xeecos/OpenNightSkyCam/Firmware/src/ll_cam.cpp

// Copyright 2010-2020 Espressif Systems (Shanghai) PTE LTD
//
// Licensed under the Apache License, Version 2.0 (the "License");
// you may not use this file except in compliance with the License.
// You may obtain a copy of the License at
//
//     http://www.apache.org/licenses/LICENSE-2.0
//
// Unless required by applicable law or agreed to in writing, software
// distributed under the License is distributed on an "AS IS" BASIS,
// WITHOUT WARRANTIES OR CONDITIONS OF ANY KIND, either express or implied.
// See the License for the specific language governing permissions and
// limitations under the License.

#include <stdio.h>
#include <string.h>
#include <Arduino.h>
#include "soc/system_reg.h"
#include "soc/lcd_cam_struct.h"
#include "soc/lcd_cam_reg.h"
#include "soc/gdma_struct.h"
#include "soc/gdma_periph.h"
#include "soc/gdma_reg.h"
#include "ll_cam.h"
#include "cam_hal.h"
#include "config.h"
#include "log.h"
#if (ESP_IDF_VERSION_MAJOR >= 5)
#define gpio_matrix_in(a, b, c) gpio_iomux_in(a, b)
#define gpio_matrix_out(a, b, c, d) gpio_iomux_out(a, b, c)
#endif
static const char *TAG = "s3 ll_cam";
static uint8_t BIT12_8[4096] = {};
static void IRAM_ATTR ll_cam_vsync_isr(void *arg)
{
    // DBG_PIN_SET(1);
    cam_obj_t *cam = (cam_obj_t *)arg;
    BaseType_t HPTaskAwoken = pdFALSE;
    uint32_t state = LCD_CAM.lc_dma_int_st.val;
    uint32_t v = LCD_CAM.lc_dma_int_st.cam_vsync_int_st;
    if (state == 0)
    {
        return;
    }
    LCD_CAM.lc_dma_int_clr.val = state;
    if (v)
    {
        ll_cam_send_event(cam, CAM_VSYNC_EVENT, &HPTaskAwoken);
    }

    if (HPTaskAwoken == pdTRUE)
    {
        portYIELD_FROM_ISR();
    }
    // DBG_PIN_SET(0);
}

static void IRAM_ATTR ll_cam_dma_isr(void *arg)
{
    cam_obj_t *cam = (cam_obj_t *)arg;
    BaseType_t HPTaskAwoken = pdFALSE;
    int state = GDMA.channel[cam->dma_num].in.int_st.val;
    int v = GDMA.channel[cam->dma_num].in.int_st.in_suc_eof;
    if (state == 0)
    {
        return;
    }
    GDMA.channel[cam->dma_num].in.int_clr.val = state;
    if (v)
    {
        ll_cam_send_event(cam, CAM_IN_SUC_EOF_EVENT, &HPTaskAwoken);
    }

    if (HPTaskAwoken == pdTRUE)
    {
        portYIELD_FROM_ISR();
    }
}

bool IRAM_ATTR ll_cam_stop(cam_obj_t *cam)
{
    GDMA.channel[cam->dma_num].in.int_ena.in_suc_eof = 0;
    GDMA.channel[cam->dma_num].in.int_clr.in_suc_eof = 0;
    GDMA.channel[cam->dma_num].in.link.stop = 1;
    return true;
}

esp_err_t ll_cam_deinit(cam_obj_t *cam)
{
    if (cam->cam_intr_handle)
    {
        esp_intr_free(cam->cam_intr_handle);
        cam->cam_intr_handle = NULL;
    }

    if (cam->dma_intr_handle)
    {
        esp_intr_free(cam->dma_intr_handle);
        cam->dma_intr_handle = NULL;
    }
    GDMA.channel[cam->dma_num].in.link.addr = 0x0;

    LCD_CAM.cam_ctrl1.cam_start = 0;
    LCD_CAM.cam_ctrl1.cam_reset = 1;
    LCD_CAM.cam_ctrl1.cam_reset = 0;
    return ESP_OK;
}

bool ll_cam_start(cam_obj_t *cam, int frame_pos)
{

    LCD_CAM.cam_ctrl1.cam_start = 0;

    GDMA.channel[cam->dma_num].in.int_clr.in_suc_eof = 1;
    GDMA.channel[cam->dma_num].in.int_ena.in_suc_eof = 1;

    LCD_CAM.cam_ctrl1.cam_reset = 1;
    LCD_CAM.cam_ctrl1.cam_reset = 0;
    LCD_CAM.cam_ctrl1.cam_afifo_reset = 1;
    LCD_CAM.cam_ctrl1.cam_afifo_reset = 0;

    GDMA.channel[cam->dma_num].in.conf0.in_rst = 1;
    GDMA.channel[cam->dma_num].in.conf0.in_rst = 0;
    
    LCD_CAM.cam_ctrl1.cam_rec_data_bytelen = cam->dma_half_buffer_size - 1; // Ping pong operation
    GDMA.channel[cam->dma_num].in.link.addr = ((uint32_t)&cam->frames[frame_pos].dma[0]) & 0xfffff;
    GDMA.channel[cam->dma_num].in.link.start = 1;

    LCD_CAM.cam_ctrl.cam_update = 1;
    LCD_CAM.cam_ctrl1.cam_start = 1;
    return true;
}

static esp_err_t ll_cam_dma_init(cam_obj_t *cam)
{
    
    for(int i=0;i<4096;i++)
    {
        BIT12_8[i] = (uint8_t)floorf(powf(2.0f,(log2f(i)*8.0f/12.0f)));
    }
    for (int x = (SOC_GDMA_PAIRS_PER_GROUP - 1); x >= 0; x--)
    {
        if (GDMA.channel[x].in.link.addr == 0x0)
        {
            cam->dma_num = x;
            // LOG_UART("DMA Channel=%d\n", cam->dma_num);
            break;
        }
        if (x == 0)
        {
            cam_deinit();
            LOG_UART("Can't found available GDMA channel");
            return ESP_FAIL;
        }
    }
    if (REG_GET_BIT(SYSTEM_PERIP_CLK_EN1_REG, SYSTEM_DMA_CLK_EN) == 0)
    {
        REG_CLR_BIT(SYSTEM_PERIP_CLK_EN1_REG, SYSTEM_DMA_CLK_EN);
        REG_SET_BIT(SYSTEM_PERIP_CLK_EN1_REG, SYSTEM_DMA_CLK_EN);
        REG_SET_BIT(SYSTEM_PERIP_RST_EN1_REG, SYSTEM_DMA_RST);
        REG_CLR_BIT(SYSTEM_PERIP_RST_EN1_REG, SYSTEM_DMA_RST);
    }

    GDMA.channel[cam->dma_num].in.int_clr.val = ~0;
    GDMA.channel[cam->dma_num].in.int_ena.val = 0;

    GDMA.channel[cam->dma_num].in.conf0.val = 0;
    GDMA.channel[cam->dma_num].in.conf0.in_rst = 1;
    GDMA.channel[cam->dma_num].in.conf0.in_rst = 0;

    GDMA.channel[cam->dma_num].in.conf1.in_check_owner = 0;

    GDMA.channel[cam->dma_num].in.peri_sel.sel = 5;
    GDMA.channel[cam->dma_num].in.pri.rx_pri = 9;//rx prio 0-15
    // GDMA.channel[cam->dma_num].in.sram_size.in_size = 6;//This register is used to configure the size of L2 Tx FIFO for Rx channel. 0:16 bytes, 1:24 bytes, 2:32 bytes, 3: 40 bytes, 4: 48 bytes, 5:56 bytes, 6: 64 bytes, 7: 72 bytes, 8: 80 bytes.
    GDMA.channel[cam->dma_num].in.wight.rx_weight = 7;//The weight of Rx channel 0-15
    return ESP_OK;
}

esp_err_t ll_cam_config(cam_obj_t *cam, const camera_config_t *config)
{
    if (REG_GET_BIT(SYSTEM_PERIP_CLK_EN1_REG, SYSTEM_LCD_CAM_CLK_EN) == 0)
    {
        REG_CLR_BIT(SYSTEM_PERIP_CLK_EN1_REG, SYSTEM_LCD_CAM_CLK_EN);
        REG_SET_BIT(SYSTEM_PERIP_CLK_EN1_REG, SYSTEM_LCD_CAM_CLK_EN);
        REG_SET_BIT(SYSTEM_PERIP_RST_EN1_REG, SYSTEM_LCD_CAM_RST);
        REG_CLR_BIT(SYSTEM_PERIP_RST_EN1_REG, SYSTEM_LCD_CAM_RST);
    }

    LCD_CAM.cam_ctrl.val = 0;

    LCD_CAM.cam_ctrl.cam_clkm_div_b = 0;
    LCD_CAM.cam_ctrl.cam_clkm_div_a = 1;
    LCD_CAM.cam_ctrl.cam_clkm_div_num = 240000000 / config->xclk_freq_hz;
    LCD_CAM.cam_ctrl.cam_clk_sel = 2;
    // Select Camera module source clock. 0: no clock. 1: APLL. 2: CLK240. 3: CLK160.

    LCD_CAM.cam_ctrl.cam_stop_en = 0;
    LCD_CAM.cam_ctrl.cam_vsync_filter_thres = 4;
    // Filter by LCD_CAM clock
    LCD_CAM.cam_ctrl.cam_update = 0;
    LCD_CAM.cam_ctrl.cam_byte_order = cam->swap_data;
    LCD_CAM.cam_ctrl.cam_bit_order = 0;
    LCD_CAM.cam_ctrl.cam_line_int_en = 0;
    LCD_CAM.cam_ctrl.cam_vs_eof_en = 0;
    // 1: CAM_VSYNC to generate in_suc_eof.
    // 0: in_suc_eof is controlled by reg_cam_rec_data_cyclelen

    LCD_CAM.cam_ctrl1.val = 0;
    LCD_CAM.cam_ctrl1.cam_rec_data_bytelen = LCD_CAM_DMA_NODE_BUFFER_MAX_SIZE - 1;
    // Cannot be assigned to 0, and it is easy to overflow
    LCD_CAM.cam_ctrl1.cam_line_int_num = 0;
    // The number of hsyncs that generate hs interrupts
    LCD_CAM.cam_ctrl1.cam_clk_inv = 0;
    LCD_CAM.cam_ctrl1.cam_vsync_filter_en = 1;
    LCD_CAM.cam_ctrl1.cam_2byte_en = config->bits>8;
    LCD_CAM.cam_ctrl1.cam_de_inv = 0;
    LCD_CAM.cam_ctrl1.cam_hsync_inv = 0;
    LCD_CAM.cam_ctrl1.cam_vsync_inv = 0;
    LCD_CAM.cam_ctrl1.cam_vh_de_mode_en = 0;
    LCD_CAM.cam_rgb_yuv.val = 0;

    LCD_CAM.cam_ctrl.cam_update = 1;
    LCD_CAM.cam_ctrl1.cam_start = 1;

    ll_cam_dma_init(cam);

    return ESP_OK;
}
void ll_xclk_stop()
{
    LCD_CAM.cam_ctrl.cam_stop_en = 1;
}
void ll_xclk_start()
{
    LCD_CAM.cam_ctrl.cam_stop_en = 0;
}
void ll_cam_vsync_intr_enable(cam_obj_t *cam, bool en)
{
    LCD_CAM.lc_dma_int_clr.cam_vsync_int_clr = 1;
    if (en)
    {
        LCD_CAM.lc_dma_int_ena.cam_vsync_int_ena = 1;
    }
    else
    {
        LCD_CAM.lc_dma_int_ena.cam_vsync_int_ena = 0;
    }
}

esp_err_t ll_cam_set_pin(cam_obj_t *cam, const camera_config_t *config)
{
    PIN_FUNC_SELECT(GPIO_PIN_MUX_REG[config->pin_pclk], PIN_FUNC_GPIO);
    gpio_set_direction((gpio_num_t)config->pin_pclk, GPIO_MODE_INPUT);
    gpio_set_pull_mode((gpio_num_t)config->pin_pclk, GPIO_FLOATING);
    gpio_matrix_in((gpio_num_t)config->pin_pclk, CAM_PCLK_IDX, false);

    PIN_FUNC_SELECT(GPIO_PIN_MUX_REG[config->pin_vsync], PIN_FUNC_GPIO);
    gpio_set_direction((gpio_num_t)config->pin_vsync, GPIO_MODE_INPUT);
    gpio_set_pull_mode((gpio_num_t)config->pin_vsync, GPIO_FLOATING);
    gpio_matrix_in((gpio_num_t)config->pin_vsync, CAM_V_SYNC_IDX, cam->vsync_invert);

    PIN_FUNC_SELECT(GPIO_PIN_MUX_REG[config->pin_href], PIN_FUNC_GPIO);
    gpio_set_direction((gpio_num_t)config->pin_href, GPIO_MODE_INPUT);
    gpio_set_pull_mode((gpio_num_t)config->pin_href, GPIO_FLOATING);
    gpio_matrix_in((gpio_num_t)config->pin_href, CAM_H_ENABLE_IDX, false);

    int data_pins[12] = {
        config->pin_d4,
        config->pin_d5,
        config->pin_d6,
        config->pin_d7,
        config->pin_d8,
        config->pin_d9,
        config->pin_d10,
        config->pin_d11
    };
    if(config->bits==12)
    {
        data_pins[0] = config->pin_d0;
        data_pins[1] = config->pin_d1;
        data_pins[2] = config->pin_d2;
        data_pins[3] = config->pin_d3;
        data_pins[4] = config->pin_d4;
        data_pins[5] = config->pin_d5;
        data_pins[6] = config->pin_d6;
        data_pins[7] = config->pin_d7;
        data_pins[8] = config->pin_d8;
        data_pins[9] = config->pin_d9;
        data_pins[10] = config->pin_d10;
        data_pins[11] = config->pin_d11;
    };
    for (int i = 0; i < config->bits; i++)
    {
        PIN_FUNC_SELECT(GPIO_PIN_MUX_REG[data_pins[i]], PIN_FUNC_GPIO);
        gpio_set_direction((gpio_num_t)data_pins[i], GPIO_MODE_INPUT);
        gpio_set_pull_mode((gpio_num_t)data_pins[i], GPIO_FLOATING);
        gpio_matrix_in(data_pins[i], CAM_DATA_IN0_IDX + i, false);
    }
    if(config->pin_xclk>-1)
    {
        PIN_FUNC_SELECT(GPIO_PIN_MUX_REG[config->pin_xclk], PIN_FUNC_GPIO);
        gpio_set_direction((gpio_num_t)config->pin_xclk, GPIO_MODE_OUTPUT);
        gpio_set_pull_mode((gpio_num_t)config->pin_xclk, GPIO_FLOATING);
        gpio_matrix_out(config->pin_xclk, CAM_CLK_IDX, false, false);

    }
    return ESP_OK;
}

esp_err_t ll_cam_init_isr(cam_obj_t *cam)
{
    esp_err_t ret = ESP_OK;
    ret = esp_intr_alloc_intrstatus(gdma_periph_signals.groups[0].pairs[cam->dma_num].rx_irq_id,
                                    ESP_INTR_FLAG_LOWMED | ESP_INTR_FLAG_SHARED | ESP_INTR_FLAG_IRAM,
                                    (uint32_t)&GDMA.channel[cam->dma_num].in.int_st, GDMA_IN_SUC_EOF_CH0_INT_ST_M,
                                    ll_cam_dma_isr, cam, &cam->dma_intr_handle);
    if (ret != ESP_OK)
    {
        LOG_UART("DMA interrupt allocation of camera failed");
        return ret;
    }

    ret = esp_intr_alloc_intrstatus(ETS_LCD_CAM_INTR_SOURCE,
                                    ESP_INTR_FLAG_LOWMED | ESP_INTR_FLAG_SHARED | ESP_INTR_FLAG_IRAM,
                                    (uint32_t)&LCD_CAM.lc_dma_int_st.val, LCD_CAM_CAM_VSYNC_INT_ST_M,
                                    ll_cam_vsync_isr, cam, &cam->cam_intr_handle);
    if (ret != ESP_OK)
    {
        LOG_UART("LCD_CAM interrupt allocation of camera failed");
        return ret;
    }
    return ESP_OK;
}

void ll_cam_do_vsync(cam_obj_t *cam)
{
    gpio_matrix_in(cam->vsync_pin, CAM_V_SYNC_IDX, !cam->vsync_invert);
    ets_delay_us(10);
    gpio_matrix_in(cam->vsync_pin, CAM_V_SYNC_IDX, cam->vsync_invert);
}

uint8_t ll_cam_get_dma_align(cam_obj_t *cam)
{
    return 16 << GDMA.channel[cam->dma_num].in.conf1.in_ext_mem_bk_size;
}

static bool ll_cam_calc_rgb_dma(cam_obj_t *cam)
{
    size_t node_max = LCD_CAM_DMA_NODE_BUFFER_MAX_SIZE / cam->dma_bytes_per_item;
    size_t line_width = cam->width * cam->in_bytes_per_pixel;
    size_t node_size = node_max;
    size_t nodes_per_line = 1;
    size_t lines_per_node = 1;

    // Calculate DMA Node Size so that it's divisable by or divisor of the line width
    if (line_width >= node_max)
    {
        // One or more nodes will be requied for one line
        for (size_t i = node_max; i > 0; i = i - 1)
        {
            if ((line_width % i) == 0)
            {
                node_size = i;
                nodes_per_line = line_width / node_size;
                break;
            }
        }
    }
    else
    {
        // One or more lines can fit into one node
        for (size_t i = node_max; i > 0; i = i - 1)
        {
            if ((i % line_width) == 0)
            {
                node_size = i;
                lines_per_node = node_size / line_width;
                while ((cam->height % lines_per_node) != 0)
                {
                    lines_per_node = lines_per_node - 1;
                    node_size = lines_per_node * line_width;
                }
                break;
            }
        }
    }

    // LOG_UART("node_size: %4u, nodes_per_line: %u, lines_per_node: %u\n", node_size * cam->dma_bytes_per_item, nodes_per_line, lines_per_node);

    cam->dma_node_buffer_size = node_size * cam->dma_bytes_per_item;

    size_t dma_half_buffer_max = CONFIG_CAMERA_DMA_BUFFER_SIZE_MAX / 2 / cam->dma_bytes_per_item;
    if (line_width > dma_half_buffer_max)
    {
        LOG_UART("Resolution too high");
        return 0;
    }

    // Calculate minimum EOF size = max(mode_size, line_size)
    size_t dma_half_buffer_min = node_size * nodes_per_line;

    // Calculate max EOF size divisable by node size
    size_t dma_half_buffer = (dma_half_buffer_max / dma_half_buffer_min) * dma_half_buffer_min;

    // Adjust EOF size so that height will be divisable by the number of lines in each EOF
    size_t lines_per_half_buffer = dma_half_buffer / line_width;
    while ((cam->height % lines_per_half_buffer) != 0)
    {
        dma_half_buffer = dma_half_buffer - dma_half_buffer_min;
        lines_per_half_buffer = dma_half_buffer / line_width;
    }

    // Calculate DMA size
    size_t dma_buffer_size = cam->recv_size / cam->dma_bytes_per_item;

    cam->dma_buffer_size = dma_buffer_size * cam->dma_bytes_per_item;
    cam->dma_half_buffer_size = dma_half_buffer * cam->dma_bytes_per_item;
    cam->dma_half_buffer_cnt = cam->dma_buffer_size / cam->dma_half_buffer_size;
    // LOG_UART("dma_half_buffer_size: %d, %d\n", dma_half_buffer, cam->dma_bytes_per_item);
    return 1;
}

bool ll_cam_dma_sizes(cam_obj_t *cam,const camera_config_t* config)
{
    cam->dma_bytes_per_item = config->bits>8?2:1;
    return ll_cam_calc_rgb_dma(cam);
}

size_t IRAM_ATTR ll_cam_memcpy(cam_obj_t *cam, uint8_t *out, const uint8_t *in, size_t len)
{
    // YUV to Grayscale
    if (cam->in_bytes_per_pixel == 2 && cam->fb_bytes_per_pixel == 1) {
        size_t end = len >> 1;
        for (size_t i = 0; i < end; ++i) {
            uint16_t v = ((in[1]&0b1111)<<8);
            v+=in[0];
            out[0] = BIT12_8[v];
            out += 1;
            in += 2;
        }
        return len>>1;
    }

    // just memcpy
    memcpy(out, in, len);
    return len;
}

esp_err_t ll_cam_set_sample_mode(cam_obj_t *cam, uint32_t xclk_freq_hz,const camera_config_t* config)
{
    cam->in_bytes_per_pixel = config->bits>8?2:1; // camera sends YU/YV
    cam->fb_bytes_per_pixel = 1; // frame buffer stores YU/YV/RGB565
    return ESP_OK;
}
