xeecos/OpenNightSkyCam/Firmware/src/sccb.cpp

#include <stdbool.h>
#include <string.h>
#include <freertos/FreeRTOS.h>
#include <freertos/task.h>
#include "sccb.h"
#include "sensor.h"
#include <stdio.h>
#include "sdkconfig.h"
#include "log.h"
#if defined(ARDUINO_ARCH_ESP32) && defined(CONFIG_ARDUHAL_ESP_LOG)
#include "esp32-hal-log.h"
#else
#include "esp_log.h"
static const char* TAG = "sccb";
#endif

#define LITTLETOBIG(x)          ((x<<8)|(x>>8))

#include "driver/i2c.h"

// support IDF 5.x
#ifndef portTICK_RATE_MS
#define portTICK_RATE_MS portTICK_PERIOD_MS
#endif

#define SCCB_FREQ               100000                /*!< I2C master frequency*/
#define WRITE_BIT               I2C_MASTER_WRITE      /*!< I2C master write */
#define READ_BIT                I2C_MASTER_READ       /*!< I2C master read */
#define ACK_CHECK_EN            0x1                   /*!< I2C master will check ack from slave*/
#define ACK_CHECK_DIS           0x0                   /*!< I2C master will not check ack from slave */
#define ACK_VAL                 (i2c_ack_type_t)0x0                   /*!< I2C ack value */
#define NACK_VAL                (i2c_ack_type_t)0x1                   /*!< I2C nack value */
#if CONFIG_SCCB_HARDWARE_I2C_PORT1
const int SCCB_I2C_PORT_DEFAULT = 1;
#else
const int SCCB_I2C_PORT_DEFAULT = 0;
#endif

static int sccb_i2c_port;
static bool sccb_owns_i2c_port;

int SCCB_Init(int pin_sda, int pin_scl)
{
    LOG_UART("pin_sda %d pin_scl %d\n", pin_sda, pin_scl);
    i2c_config_t conf;
    esp_err_t ret;

    memset(&conf, 0, sizeof(i2c_config_t));

    sccb_i2c_port = SCCB_I2C_PORT_DEFAULT;
    sccb_owns_i2c_port = true;
    LOG_UART("sccb_i2c_port=%d\n", sccb_i2c_port);

    conf.mode = I2C_MODE_MASTER;
    conf.sda_io_num = pin_sda;
    conf.sda_pullup_en = GPIO_PULLUP_ENABLE;
    conf.scl_io_num = pin_scl;
    conf.scl_pullup_en = GPIO_PULLUP_ENABLE;
    conf.master.clk_speed = SCCB_FREQ;

    if ((ret =  i2c_param_config(sccb_i2c_port, &conf)) != ESP_OK) {
        return ret;
    }

    return i2c_driver_install(sccb_i2c_port, conf.mode, 0, 0, 0);
}

int SCCB_Use_Port(int i2c_num) { // sccb use an already initialized I2C port
    if (sccb_owns_i2c_port) {
        SCCB_Deinit();
    }
    if (i2c_num < 0 || i2c_num > I2C_NUM_MAX) {
        return ESP_ERR_INVALID_ARG;
    }
    sccb_i2c_port = i2c_num;
    return ESP_OK;
}

int SCCB_Deinit(void)
{
    if (!sccb_owns_i2c_port) {
        return ESP_OK;
    }
    sccb_owns_i2c_port = false;
    return i2c_driver_delete(sccb_i2c_port);
}

uint8_t SCCB_Probe(void)
{
    uint8_t slave_addr = 0x0;

    for (size_t i = 0; i < CAMERA_MODEL_MAX; i++) {
        if (slave_addr == camera_sensor[i].sccb_addr) {
            continue;
        }
        slave_addr = camera_sensor[i].sccb_addr;
        i2c_cmd_handle_t cmd = i2c_cmd_link_create();
        i2c_master_start(cmd);
        i2c_master_write_byte(cmd, ( slave_addr << 1 ) | WRITE_BIT, ACK_CHECK_EN);
        i2c_master_stop(cmd);
        esp_err_t ret = i2c_master_cmd_begin(sccb_i2c_port, cmd, 1000 / portTICK_RATE_MS);
        i2c_cmd_link_delete(cmd);
        if( ret == ESP_OK) {
            return slave_addr;
        }
        vTaskDelay(10/portTICK_RATE_MS);
    }
    return 0;
}

uint8_t SCCB_Read(uint8_t slv_addr, uint8_t reg)
{
    uint8_t data=0;
    esp_err_t ret = ESP_FAIL;
    i2c_cmd_handle_t cmd = i2c_cmd_link_create();
    i2c_master_start(cmd);
    i2c_master_write_byte(cmd, ( slv_addr << 1 ) | WRITE_BIT, ACK_CHECK_EN);
    i2c_master_write_byte(cmd, reg, ACK_CHECK_EN);
    i2c_master_stop(cmd);
    ret = i2c_master_cmd_begin(sccb_i2c_port, cmd, 1000 / portTICK_RATE_MS);
    i2c_cmd_link_delete(cmd);
    if(ret != ESP_OK) return -1;
    cmd = i2c_cmd_link_create();
    i2c_master_start(cmd);
    i2c_master_write_byte(cmd, ( slv_addr << 1 ) | READ_BIT, ACK_CHECK_EN);
    i2c_master_read_byte(cmd, &data, NACK_VAL);
    i2c_master_stop(cmd);
    ret = i2c_master_cmd_begin(sccb_i2c_port, cmd, 1000 / portTICK_RATE_MS);
    i2c_cmd_link_delete(cmd);
    if(ret != ESP_OK) {
        LOG_UART( "SCCB_Read Failed addr:0x%02x, reg:0x%02x, data:0x%02x, ret:%d\n", slv_addr, reg, data, ret);
    }
    return data;
}

uint8_t SCCB_Write(uint8_t slv_addr, uint8_t reg, uint8_t data)
{
    esp_err_t ret = ESP_FAIL;
    i2c_cmd_handle_t cmd = i2c_cmd_link_create();
    i2c_master_start(cmd);
    i2c_master_write_byte(cmd, ( slv_addr << 1 ) | WRITE_BIT, ACK_CHECK_EN);
    i2c_master_write_byte(cmd, reg, ACK_CHECK_EN);
    i2c_master_write_byte(cmd, data, ACK_CHECK_EN);
    i2c_master_stop(cmd);
    ret = i2c_master_cmd_begin(sccb_i2c_port, cmd, 1000 / portTICK_RATE_MS);
    i2c_cmd_link_delete(cmd);
    if(ret != ESP_OK) {
        LOG_UART( "SCCB_Write Failed addr:0x%02x, reg:0x%02x, data:0x%02x, ret:%d\n", slv_addr, reg, data, ret);
    }
    return ret == ESP_OK ? 0 : -1;
}

uint8_t SCCB_Read16(uint8_t slv_addr, uint16_t reg)
{
    uint8_t data=0;
    esp_err_t ret = ESP_FAIL;
    uint16_t reg_htons = LITTLETOBIG(reg);
    uint8_t *reg_u8 = (uint8_t *)&reg_htons;
    i2c_cmd_handle_t cmd = i2c_cmd_link_create();
    i2c_master_start(cmd);
    i2c_master_write_byte(cmd, ( slv_addr << 1 ) | WRITE_BIT, ACK_CHECK_EN);
    i2c_master_write_byte(cmd, reg_u8[0], ACK_CHECK_EN);
    i2c_master_write_byte(cmd, reg_u8[1], ACK_CHECK_EN);
    i2c_master_stop(cmd);
    ret = i2c_master_cmd_begin(sccb_i2c_port, cmd, 1000 / portTICK_RATE_MS);
    i2c_cmd_link_delete(cmd);
    if(ret != ESP_OK) return -1;
    cmd = i2c_cmd_link_create();
    i2c_master_start(cmd);
    i2c_master_write_byte(cmd, ( slv_addr << 1 ) | READ_BIT, ACK_CHECK_EN);
    i2c_master_read_byte(cmd, &data, NACK_VAL);
    i2c_master_stop(cmd);
    ret = i2c_master_cmd_begin(sccb_i2c_port, cmd, 1000 / portTICK_RATE_MS);
    i2c_cmd_link_delete(cmd);
    if(ret != ESP_OK) {
        LOG_UART( "W [%04x]=%02x fail\n", reg, data);
    }
    return data;
}

uint16_t SCCB_Read16_16(uint8_t slv_addr, uint16_t reg)
{
    uint8_t dataH=0,dataL=0;
    esp_err_t ret = ESP_FAIL;
    uint16_t reg_htons = LITTLETOBIG(reg);
    uint8_t *reg_u8 = (uint8_t *)&reg_htons;
    i2c_cmd_handle_t cmd = i2c_cmd_link_create();
    i2c_master_start(cmd);
    i2c_master_write_byte(cmd, ( slv_addr << 1 ) | WRITE_BIT, ACK_CHECK_EN);
    i2c_master_write_byte(cmd, reg_u8[0], ACK_CHECK_EN);
    i2c_master_write_byte(cmd, reg_u8[1], ACK_CHECK_EN);
    i2c_master_stop(cmd);
    ret = i2c_master_cmd_begin(sccb_i2c_port, cmd, 1000 / portTICK_RATE_MS);
    i2c_cmd_link_delete(cmd);
    if(ret != ESP_OK) return -1;
    cmd = i2c_cmd_link_create();
    i2c_master_start(cmd);
    i2c_master_write_byte(cmd, ( slv_addr << 1 ) | READ_BIT, ACK_CHECK_EN);
    uint16_t result = 0;
    i2c_master_read_byte(cmd, &dataH, ACK_VAL);
    i2c_master_read_byte(cmd, &dataL, NACK_VAL);
    i2c_master_stop(cmd);
    ret = i2c_master_cmd_begin(sccb_i2c_port, cmd, 1000 / portTICK_RATE_MS);
    i2c_cmd_link_delete(cmd);
    result = dataH<<8;
    result += dataL;
    return result;
}
uint8_t SCCB_Write16(uint8_t slv_addr, uint16_t reg, uint8_t data)
{
    static uint16_t i = 0;
    esp_err_t ret = ESP_FAIL;
    uint16_t reg_htons = LITTLETOBIG(reg);
    uint8_t *reg_u8 = (uint8_t *)&reg_htons;
    i2c_cmd_handle_t cmd = i2c_cmd_link_create();
    i2c_master_start(cmd);
    i2c_master_write_byte(cmd, ( slv_addr << 1 ) | WRITE_BIT, ACK_CHECK_EN);
    i2c_master_write_byte(cmd, reg_u8[0], ACK_CHECK_EN);
    i2c_master_write_byte(cmd, reg_u8[1], ACK_CHECK_EN);
    i2c_master_write_byte(cmd, data, ACK_CHECK_EN);
    i2c_master_stop(cmd);
    ret = i2c_master_cmd_begin(sccb_i2c_port, cmd, 1000 / portTICK_RATE_MS);
    i2c_cmd_link_delete(cmd);
    if(ret != ESP_OK) {
        LOG_UART( "W [%04x]=%02x %d fail\n", reg, data, i++);
    }
    return ret == ESP_OK ? 0 : -1;
}
uint8_t SCCB_Write16_16(uint8_t slv_addr, uint16_t reg, uint16_t data)
{
    static uint16_t i = 0;
    esp_err_t ret = ESP_FAIL;
    uint16_t reg_htons = LITTLETOBIG(reg);
    uint8_t *reg_u8 = (uint8_t *)&reg_htons;
    uint16_t data_htons = LITTLETOBIG(data);
    uint8_t *data_u8 = (uint8_t *)&data_htons;
    i2c_cmd_handle_t cmd = i2c_cmd_link_create();
    i2c_master_start(cmd);
    i2c_master_write_byte(cmd, ( slv_addr << 1 ) | WRITE_BIT, ACK_CHECK_EN);
    i2c_master_write_byte(cmd, reg_u8[0], ACK_CHECK_EN);
    i2c_master_write_byte(cmd, reg_u8[1], ACK_CHECK_EN);
    i2c_master_write_byte(cmd, data_u8[0], ACK_CHECK_EN);
    i2c_master_write_byte(cmd, data_u8[1], ACK_CHECK_EN);
    i2c_master_stop(cmd);
    ret = i2c_master_cmd_begin(sccb_i2c_port, cmd, 1000 / portTICK_RATE_MS);
    i2c_cmd_link_delete(cmd);
    if(ret != ESP_OK) {
        LOG_UART( "W [%04x]=%02x %d fail\n", reg, data, i++);
    }
    return ret == ESP_OK ? 0 : -1;
}
