xeecos/OpenNightSkyCam/Firmware/src/esp_camera.h

#pragma once

#include "esp_err.h"
#include "driver/ledc.h"
#include "sys/time.h"
#include "sensor.h"
/**
 * @brief Configuration structure for camera initialization
 */
typedef enum {
    CAMERA_GRAB_WHEN_EMPTY,         /*!< Fills buffers when they are empty. Less resources but first 'fb_count' frames might be old */
    CAMERA_GRAB_LATEST              /*!< Except when 1 frame buffer is used, queue will always contain the last 'fb_count' frames */
} camera_grab_mode_t;

/**
 * @brief Camera frame buffer location 
 */
typedef enum {
    CAMERA_FB_IN_PSRAM,         /*!< Frame buffer is placed in external PSRAM */
    CAMERA_FB_IN_DRAM           /*!< Frame buffer is placed in internal DRAM */
} camera_fb_location_t;

/**
 * @brief Configuration structure for camera initialization
 */
typedef struct {
    int pin_pwdn;                   /*!< GPIO pin for camera power down line */
    int pin_reset;                  /*!< GPIO pin for camera reset line */
    int pin_xclk;                   /*!< GPIO pin for camera XCLK line */
    int pin_sccb_sda;               /*!< GPIO pin for camera SDA line */
    int pin_sccb_scl;               /*!< GPIO pin for camera SCL line */
    int pin_d11; 
    int pin_d10; 
    int pin_d9; 
    int pin_d8; 
    int pin_d7;                     /*!< GPIO pin for camera D7 line */
    int pin_d6;                     /*!< GPIO pin for camera D6 line */
    int pin_d5;                     /*!< GPIO pin for camera D5 line */
    int pin_d4;                     /*!< GPIO pin for camera D4 line */
    int pin_d3;                     /*!< GPIO pin for camera D3 line */
    int pin_d2;                     /*!< GPIO pin for camera D2 line */
    int pin_d1;                     /*!< GPIO pin for camera D1 line */
    int pin_d0;                     /*!< GPIO pin for camera D0 line */
    int pin_vsync;                  /*!< GPIO pin for camera VSYNC line */
    int pin_href;                   /*!< GPIO pin for camera HREF line */
    int pin_pclk;                   /*!< GPIO pin for camera PCLK line */
    int xclk_freq_hz;               /*!< Frequency of XCLK signal, in Hz. EXPERIMENTAL: Set to 16MHz on ESP32-S2 or ESP32-S3 to enable EDMA mode */

    ledc_timer_t ledc_timer;        /*!< LEDC timer to be used for generating XCLK  */
    ledc_channel_t ledc_channel;    /*!< LEDC channel to be used for generating XCLK  */

    pixformat_t pixel_format;       /*!< Format of the pixel data: PIXFORMAT_ + YUV422|GRAYSCALE|RGB565|JPEG  */
    framesize_t frame_size;         /*!< Size of the output image: FRAMESIZE_ + QVGA|CIF|VGA|SVGA|XGA|SXGA|UXGA  */
    int bits;
    int jpeg_quality;               /*!< Quality of JPEG output. 0-63 lower means higher quality  */
    size_t fb_count;                /*!< Number of frame buffers to be allocated. If more than one, then each frame will be acquired (double speed)  */
    camera_fb_location_t fb_location; /*!< The location where the frame buffer will be allocated */
    camera_grab_mode_t grab_mode;   /*!< When buffers should be filled */
} camera_config_t;

/**
 * @brief Data structure of camera frame buffer
 */
typedef struct {
    uint8_t * buf;              /*!< Pointer to the pixel data */
    int len;                 /*!< Length of the buffer in bytes */
    size_t width;               /*!< Width of the buffer in pixels */
    size_t height;              /*!< Height of the buffer in pixels */
    struct timeval timestamp;   /*!< Timestamp since boot of the first DMA buffer of the frame */
} camera_fb_t;

#define ESP_ERR_CAMERA_BASE 0x20000
#define ESP_ERR_CAMERA_NOT_DETECTED             (ESP_ERR_CAMERA_BASE + 1)
#define ESP_ERR_CAMERA_FAILED_TO_SET_FRAME_SIZE (ESP_ERR_CAMERA_BASE + 2)
#define ESP_ERR_CAMERA_FAILED_TO_SET_OUT_FORMAT (ESP_ERR_CAMERA_BASE + 3)
#define ESP_ERR_CAMERA_NOT_SUPPORTED            (ESP_ERR_CAMERA_BASE + 4)

/**
 * @brief Initialize the camera driver
 *
 * @note call camera_probe before calling this function
 *
 * This function detects and configures camera over I2C interface,
 * allocates framebuffer and DMA buffers,
 * initializes parallel I2S input, and sets up DMA descriptors.
 *
 * Currently this function can only be called once and there is
 * no way to de-initialize this module.
 *
 * @param config  Camera configuration parameters
 *
 * @return ESP_OK on success
 */
esp_err_t ez_camera_init( camera_config_t* config);

/**
 * @brief Deinitialize the camera driver
 *
 * @return
 *      - ESP_OK on success
 *      - ESP_ERR_INVALID_STATE if the driver hasn't been initialized yet
 */
esp_err_t ez_camera_deinit();

/**
 * @brief Obtain pointer to a frame buffer.
 *
 * @return pointer to the frame buffer
 */
camera_fb_t* esp_camera_fb_get();

/**
 * @brief Return the frame buffer to be reused again.
 *
 * @param fb    Pointer to the frame buffer
 */
void esp_camera_fb_return(camera_fb_t * fb);

/**
 * @brief Get a pointer to the image sensor control structure
 *
 * @return pointer to the sensor
 */
sensor_t * esp_camera_sensor_get();
